HarshitRaj3007/EDL2024/EDL_merged_code/uart_jtag/uart_jtag_inst.v

	uart_jtag u0 (
		.avalon_jtag_slave_chipselect  (<connected-to-avalon_jtag_slave_chipselect>),  // avalon_jtag_slave.chipselect
		.avalon_jtag_slave_address     (<connected-to-avalon_jtag_slave_address>),     //                  .address
		.avalon_jtag_slave_read_n      (<connected-to-avalon_jtag_slave_read_n>),      //                  .read_n
		.avalon_jtag_slave_readdata    (<connected-to-avalon_jtag_slave_readdata>),    //                  .readdata
		.avalon_jtag_slave_write_n     (<connected-to-avalon_jtag_slave_write_n>),     //                  .write_n
		.avalon_jtag_slave_writedata   (<connected-to-avalon_jtag_slave_writedata>),   //                  .writedata
		.avalon_jtag_slave_waitrequest (<connected-to-avalon_jtag_slave_waitrequest>), //                  .waitrequest
		.clk_clk                       (<connected-to-clk_clk>),                       //               clk.clk
		.irq_irq                       (<connected-to-irq_irq>),                       //               irq.irq
		.reset_reset_n                 (<connected-to-reset_reset_n>)                  //             reset.reset_n
	);
