HarshitRaj3007/EDL2024/EDL_merged_code/uart_jtag/uart_jtag_inst.vhd

	component uart_jtag is
		port (
			avalon_jtag_slave_chipselect  : in  std_logic                     := 'X';             -- chipselect
			avalon_jtag_slave_address     : in  std_logic                     := 'X';             -- address
			avalon_jtag_slave_read_n      : in  std_logic                     := 'X';             -- read_n
			avalon_jtag_slave_readdata    : out std_logic_vector(31 downto 0);                    -- readdata
			avalon_jtag_slave_write_n     : in  std_logic                     := 'X';             -- write_n
			avalon_jtag_slave_writedata   : in  std_logic_vector(31 downto 0) := (others => 'X'); -- writedata
			avalon_jtag_slave_waitrequest : out std_logic;                                        -- waitrequest
			clk_clk                       : in  std_logic                     := 'X';             -- clk
			irq_irq                       : out std_logic;                                        -- irq
			reset_reset_n                 : in  std_logic                     := 'X'              -- reset_n
		);
	end component uart_jtag;

	u0 : component uart_jtag
		port map (
			avalon_jtag_slave_chipselect  => CONNECTED_TO_avalon_jtag_slave_chipselect,  -- avalon_jtag_slave.chipselect
			avalon_jtag_slave_address     => CONNECTED_TO_avalon_jtag_slave_address,     --                  .address
			avalon_jtag_slave_read_n      => CONNECTED_TO_avalon_jtag_slave_read_n,      --                  .read_n
			avalon_jtag_slave_readdata    => CONNECTED_TO_avalon_jtag_slave_readdata,    --                  .readdata
			avalon_jtag_slave_write_n     => CONNECTED_TO_avalon_jtag_slave_write_n,     --                  .write_n
			avalon_jtag_slave_writedata   => CONNECTED_TO_avalon_jtag_slave_writedata,   --                  .writedata
			avalon_jtag_slave_waitrequest => CONNECTED_TO_avalon_jtag_slave_waitrequest, --                  .waitrequest
			clk_clk                       => CONNECTED_TO_clk_clk,                       --               clk.clk
			irq_irq                       => CONNECTED_TO_irq_irq,                       --               irq.irq
			reset_reset_n                 => CONNECTED_TO_reset_reset_n                  --             reset.reset_n
		);
